cybernano96/trackuino/Tracker_DRA818V/trackuino/aprs.cpp

/* trackuino copyright (C) 2010  EA5HAV Javi
 *
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
 * You should have received a copy of the GNU General Public License
 * along with this program; if not, write to the Free Software
 * Foundation, Inc., 51 Franklin Street, Fifth Floor, Boston, MA  02110-1301, USA.
 */

#include "config.h"
#include "ax25.h"
#include "gps.h"
#include "aprs.h"
#include "sensors_avr.h"
#include "sensors_pic32.h"
#include "pin.h"
#include <stdio.h>
#include <stdlib.h>
#if (ARDUINO + 1) >= 100
#  include <Arduino.h>
#else
#  include <WProgram.h>
#endif

// Module functions
float meters_to_feet(float m)
{
  // 10000 ft = 3048 m
  return m / 0.3048;
}

// Exported functions
void aprs_send()
{
  //pin_write(RPD, HIGH);
  //delay(500);
  char temp[12];                   // Temperature (int/ext)
  const struct s_address addresses[] = { 
    {D_CALLSIGN, D_CALLSIGN_ID},  // Destination callsign
    {S_CALLSIGN, S_CALLSIGN_ID},  // Source callsign (-11 = balloon, -9 = car)
#ifdef DIGI_PATH1
    {DIGI_PATH1, DIGI_PATH1_TTL}, // Digi1 (first digi in the chain)
#endif
#ifdef DIGI_PATH2
    {DIGI_PATH2, DIGI_PATH2_TTL}, // Digi2 (second digi in the chain)
#endif
  };

  ax25_send_header(addresses, sizeof(addresses)/sizeof(s_address));
  ax25_send_byte('/');                // Report w/ timestamp, no APRS messaging. $ = NMEA raw data
  // ax25_send_string("021709z");     // 021709z = 2nd day of the month, 17:09 zulu (UTC/GMT)
 #ifdef DEBUG_PROT
  ax25_send_string("021709z");
 #else
  ax25_send_string(gps_time);         // 170915 = 17h:09m:15s zulu (not allowed in Status Reports)
 #endif
  ax25_send_byte('h');
  //if (fixOnce) {
 #ifdef DEBUG_PROT
  ax25_send_string(START_LAT);
 #else
  ax25_send_string(gps_aprs_lat);     // Lat: 38deg and 22.20 min (.20 are NOT seconds, but 1/100th of minutes)
 #endif
  //} else {
  //  ax25_send_string(START_LAT);
  //}
  ax25_send_byte('/');                // Symbol table
  //if (fixOnce) {
 #ifdef DEBUG_PROT
  ax25_send_string(START_LON);
 #else
  ax25_send_string(gps_aprs_lon);     // Lon: 000deg and 25.80 min
 #endif
  //} else {
  //  ax25_send_string(START_LON);
  //}
  ax25_send_byte(APRS_SYMBOL);                // Symbol: O=balloon, -=QTH
 #ifdef SENSORS
  snprintf(temp, 4, "%03d", (int)(gps_course + 0.5)); 
  ax25_send_string(temp);             // Course (degrees)
  ax25_send_byte('/');                // and
  snprintf(temp, 4, "%03d", (int)(gps_speed + 0.5));
  ax25_send_string(temp);             // speed (knots)
  ax25_send_string("/A=");            // Altitude (feet). Goes anywhere in the comment area
  snprintf(temp, 7, "%06ld", (long)(meters_to_feet(gps_altitude) + 0.5));
  ax25_send_string(temp);
  ax25_send_string("/Ti=");
  snprintf(temp, 6, "%d", sensors_int_lm60());
  ax25_send_string(temp);
  ax25_send_string("/Te=");
  snprintf(temp, 6, "%d", sensors_ext_lm60());
  ax25_send_string(temp);
  ax25_send_string("/V=");
  snprintf(temp, 6, "%d", sensors_vin());
  ax25_send_string(temp);
 #endif
  ax25_send_byte(' ');
  //if (fixNow) {
  ax25_send_string(APRS_COMMENT);     // Comment
  //} else {
  //  ax25_send_string(APRS_COMMENT_NOFIX);     // Comment
  //}
  ax25_send_footer();

  ax25_flush_frame();                 // Tell the modem to go
}
